dpmlli/Rainette/SW/Rainette/rainette_main.cpp

//  rainette_main.cpp
//  project : Rainette
//  author : Damien Pomelli 
//  last modified : 2025-07-24

#include "rainette_utils.h"
#include "rainette_event_handlers.h"


int main()
{
    start_rainette();
}
